jaygreco/ParkingPal/CAD/SMU_pcb.SLDPRT

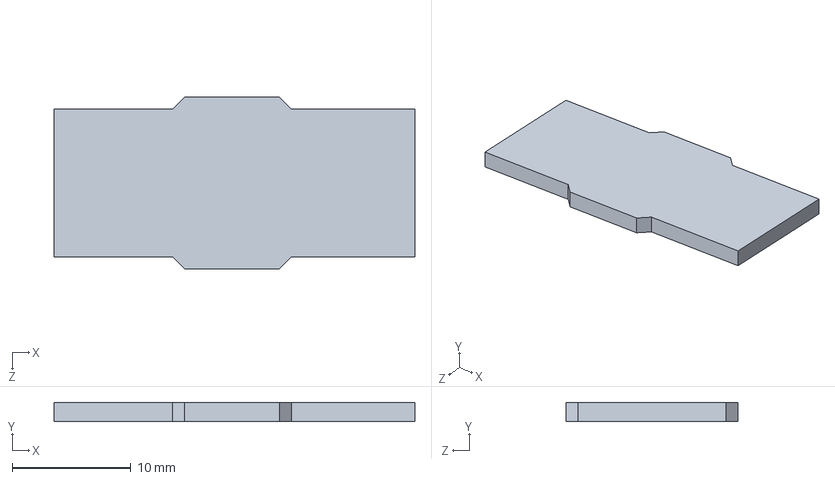
[picture p15: CAD file, 2019-02-10]
CAD/SMU_pcb.SLDPRT
30.4 x 1.62 x 14.4 mm
