jaygreco/ParkingPal/CAD/HC-SR04/Transducer.SLDPRT

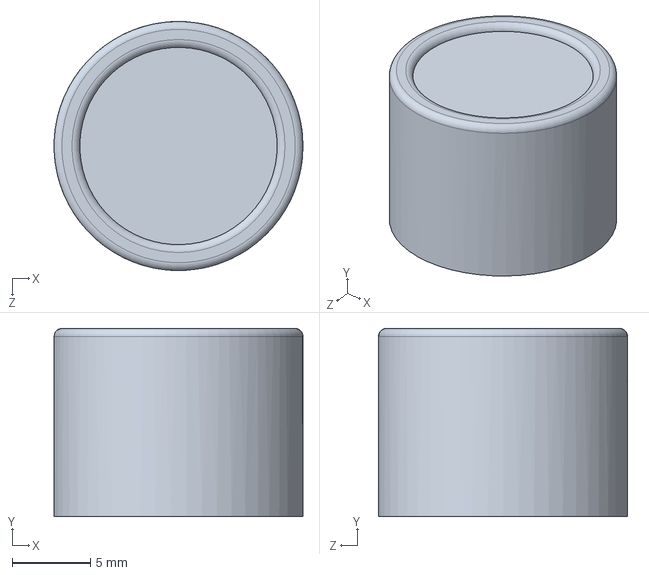
[picture p16: CAD file, 2019-02-10]
CAD/HC-SR04/Transducer.SLDPRT
15.9 x 12.0 x 15.9 mm
