jaygreco/ParkingPal/CAD/USB-A.SLDPRT

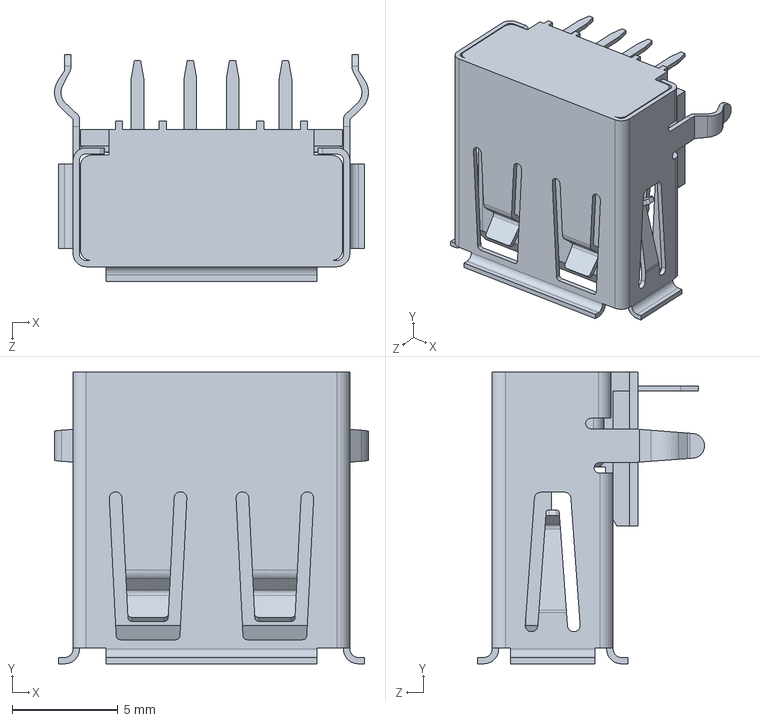
[picture p17: CAD file, 2019-02-10]
CAD/USB-A.SLDPRT
14.9 x 13.8 x 10.7 mm
