jaygreco/ParkingPal/CAD/HC-SR04/PCB.SLDPRT

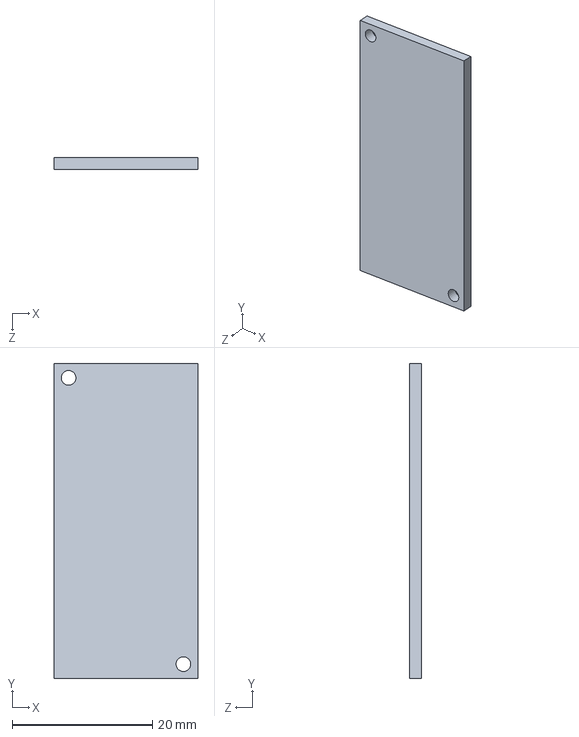
[picture p18: CAD file, 2019-02-10]
CAD/HC-SR04/PCB.SLDPRT
20.5 x 45.0 x 1.75 mm
