jaygreco/ParkingPal/CAD/MCU_pcb.SLDPRT

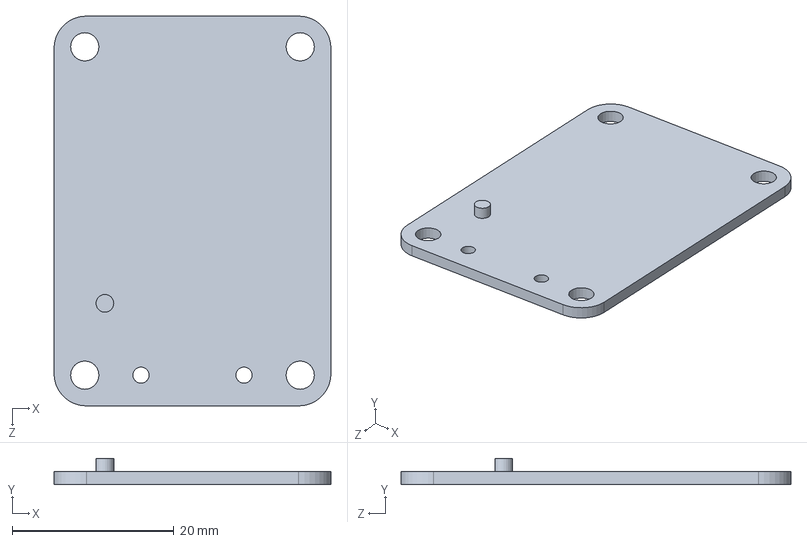
[picture p19: CAD file, 2019-02-10]
CAD/MCU_pcb.SLDPRT
34.3 x 3.22 x 48.3 mm
