jaygreco/ParkingPal/CAD/Case_bottom.SLDPRT

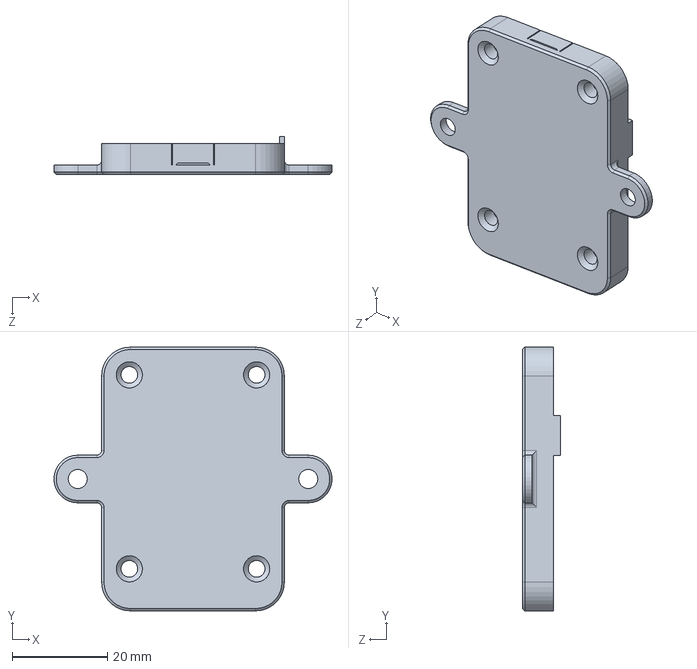
[picture p20: CAD file, 2019-02-10]
CAD/Case_bottom.SLDPRT
58.2 x 55.3 x 8.00 mm
