jaygreco/ParkingPal/CAD/hcSTP.SLDPRT

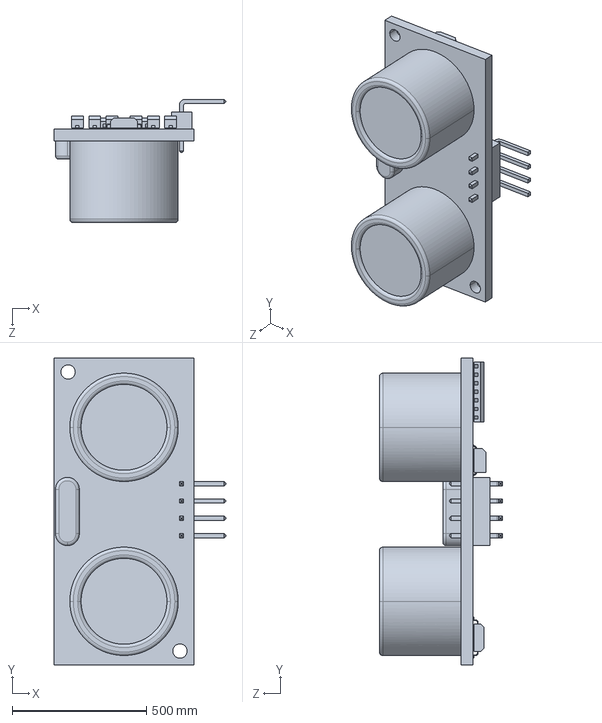
[picture p21: CAD file, 2019-02-10]
CAD/hcSTP.SLDPRT
639.6 x 1143.0 x 458.9 mm
