jaygreco/ParkingPal/CAD/SMU_case_bottom.SLDPRT

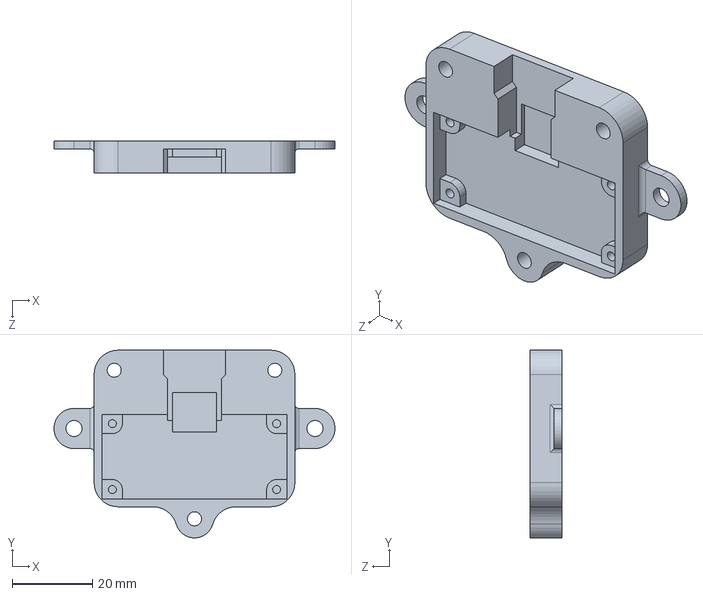
[picture p22: CAD file, 2019-02-10]
CAD/SMU_case_bottom.SLDPRT
70.0 x 46.7 x 8.00 mm
