jaygreco/ParkingPal/CAD/Buzzer.SLDPRT

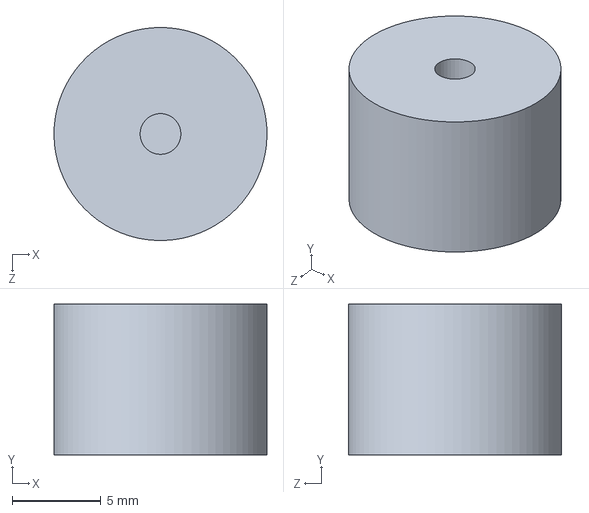
[picture p23: CAD file, 2019-02-10]
CAD/Buzzer.SLDPRT
12.0 x 8.50 x 12.0 mm
